embeddedos-org/eos-stack-manifest/docs/screenshots/efab_android_ui.png

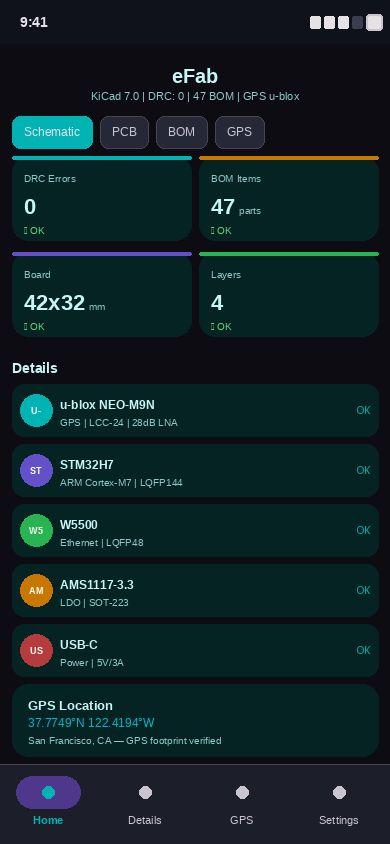
docs/screenshots/efab_android_ui.png
